TailsmanDesign/PocketMage_PDA/Resources/Assets/Calendar/calendar00.bmp

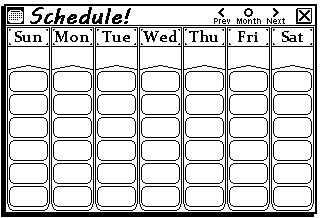
Resources/Assets/Calendar/calendar00.bmp
