TailsmanDesign/PocketMage_PDA/Resources/Assets/Calendar/calendar03.bmp

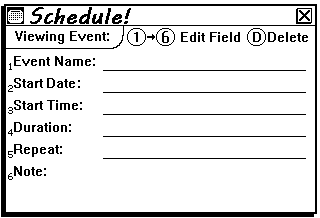
Resources/Assets/Calendar/calendar03.bmp
