TailsmanDesign/PocketMage_PDA/Resources/Assets/Calendar/calendar04.bmp

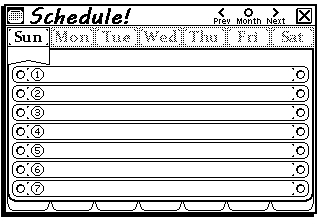
Resources/Assets/Calendar/calendar04.bmp
