TailsmanDesign/PocketMage_PDA/Resources/Assets/File Wizard/fileWiz1.bmp

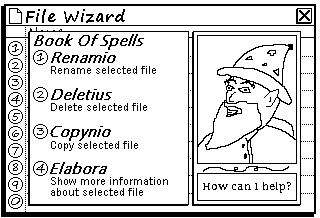
Resources/Assets/File Wizard/fileWiz1.bmp
