TailsmanDesign/PocketMage_PDA/Resources/Assets/File Wizard/fileWiz2.bmp

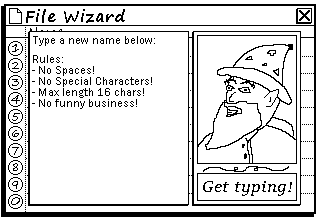
Resources/Assets/File Wizard/fileWiz2.bmp
