TailsmanDesign/PocketMage_PDA/Resources/Assets/File Wizard/fileWizLite0.bmp

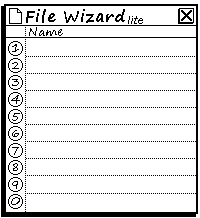
Resources/Assets/File Wizard/fileWizLite0.bmp
