TailsmanDesign/PocketMage_PDA/Resources/Assets/File Wizard/fileWizLite1.bmp

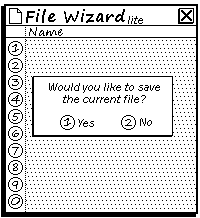
Resources/Assets/File Wizard/fileWizLite1.bmp
