TailsmanDesign/PocketMage_PDA/Resources/Assets/File Wizard/fileWizLite2.bmp

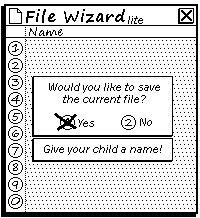
Resources/Assets/File Wizard/fileWizLite2.bmp
