TailsmanDesign/PocketMage_PDA/Resources/Assets/Font Czar/font0.bmp

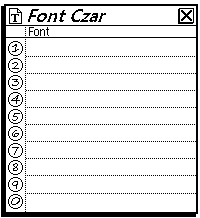
Resources/Assets/Font Czar/font0.bmp
