TailsmanDesign/PocketMage_PDA/Resources/Assets/Onboarding/onboardMage.png

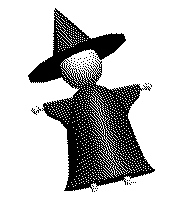
Resources/Assets/Onboarding/onboardMage.png
