TailsmanDesign/PocketMage_PDA/Resources/Assets/ScreenSaver/New folder/appzap_Omiopi.bmp

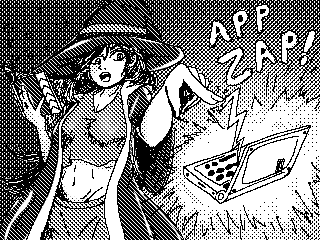
Resources/Assets/ScreenSaver/New folder/appzap_Omiopi.bmp
