TailsmanDesign/PocketMage_PDA/Resources/Assets/ScreenSaver/New folder/betterworld_JosieBB.bmp

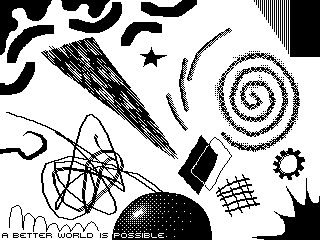
Resources/Assets/ScreenSaver/New folder/betterworld_JosieBB.bmp
