TailsmanDesign/PocketMage_PDA/Resources/Assets/ScreenSaver/New folder/castle_Nora.bmp

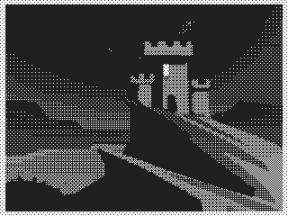
Resources/Assets/ScreenSaver/New folder/castle_Nora.bmp
