TailsmanDesign/PocketMage_PDA/Resources/Assets/ScreenSaver/New folder/chad_rein.bmp

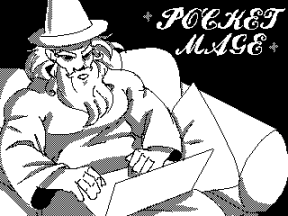
Resources/Assets/ScreenSaver/New folder/chad_rein.bmp
