TailsmanDesign/PocketMage_PDA/Resources/Assets/ScreenSaver/New folder/classic (1).bmp

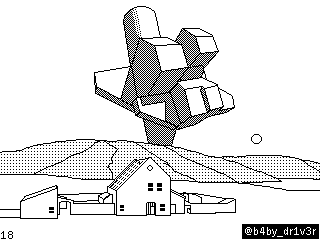
Resources/Assets/ScreenSaver/New folder/classic (1).bmp
