TailsmanDesign/PocketMage_PDA/Resources/Assets/ScreenSaver/New folder/classic (2).bmp

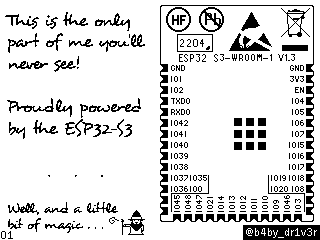
Resources/Assets/ScreenSaver/New folder/classic (2).bmp
