TailsmanDesign/PocketMage_PDA/Resources/Assets/ScreenSaver/New folder/classic (3).bmp

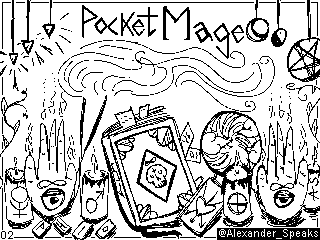
Resources/Assets/ScreenSaver/New folder/classic (3).bmp
