TailsmanDesign/PocketMage_PDA/Resources/Assets/ScreenSaver/New folder/classic (5).bmp

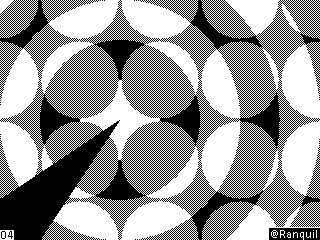
Resources/Assets/ScreenSaver/New folder/classic (5).bmp
