TailsmanDesign/PocketMage_PDA/Resources/Assets/ScreenSaver/New folder/classic (6).bmp

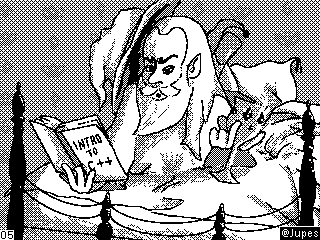
Resources/Assets/ScreenSaver/New folder/classic (6).bmp
