TailsmanDesign/PocketMage_PDA/Resources/Assets/ScreenSaver/New folder/classic (7).bmp

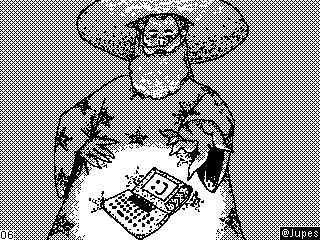
Resources/Assets/ScreenSaver/New folder/classic (7).bmp
