TailsmanDesign/PocketMage_PDA/Resources/Assets/ScreenSaver/New folder/classic (8).bmp

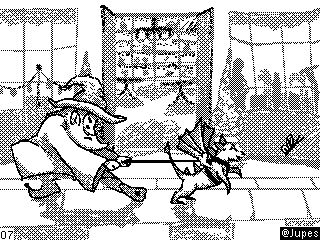
Resources/Assets/ScreenSaver/New folder/classic (8).bmp
