TailsmanDesign/PocketMage_PDA/Resources/Assets/ScreenSaver/New folder/classic (9).bmp

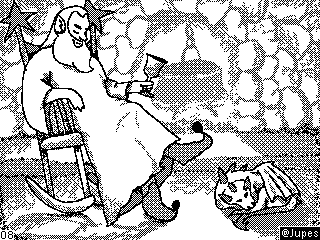
Resources/Assets/ScreenSaver/New folder/classic (9).bmp
