TailsmanDesign/PocketMage_PDA/Resources/Assets/ScreenSaver/New folder/classic (10).bmp

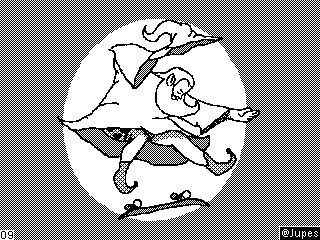
Resources/Assets/ScreenSaver/New folder/classic (10).bmp
