TailsmanDesign/PocketMage_PDA/Resources/Assets/ScreenSaver/New folder/classic (11).bmp

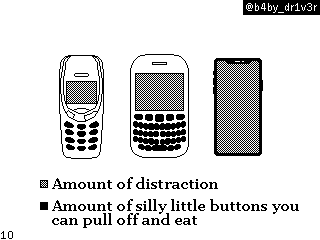
Resources/Assets/ScreenSaver/New folder/classic (11).bmp
