TailsmanDesign/PocketMage_PDA/Resources/Assets/ScreenSaver/New folder/classic (13).bmp

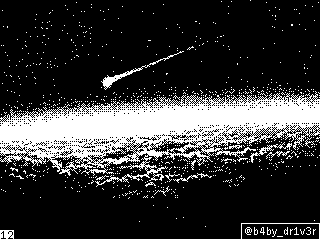
Resources/Assets/ScreenSaver/New folder/classic (13).bmp
