TailsmanDesign/PocketMage_PDA/Resources/Assets/ScreenSaver/New folder/classic (14).bmp

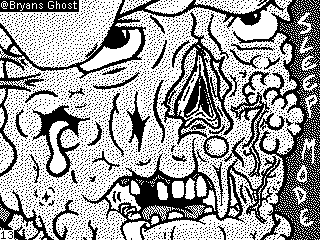
Resources/Assets/ScreenSaver/New folder/classic (14).bmp
