TailsmanDesign/PocketMage_PDA/Resources/Assets/ScreenSaver/New folder/classic (15).bmp

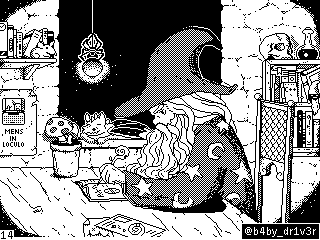
Resources/Assets/ScreenSaver/New folder/classic (15).bmp
