TailsmanDesign/PocketMage_PDA/Resources/Assets/ScreenSaver/New folder/classic (18).bmp

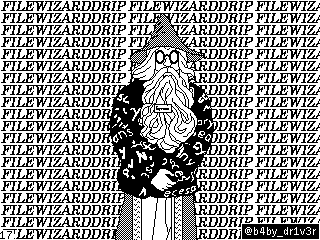
Resources/Assets/ScreenSaver/New folder/classic (18).bmp
