TailsmanDesign/PocketMage_PDA/Resources/Assets/ScreenSaver/New folder/dragon_TheOddFireFox.bmp

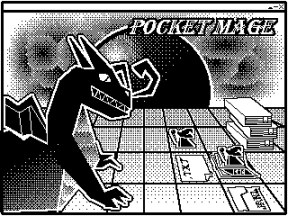
Resources/Assets/ScreenSaver/New folder/dragon_TheOddFireFox.bmp
