TailsmanDesign/PocketMage_PDA/Resources/Assets/ScreenSaver/New folder/mage_GusCosta.bmp

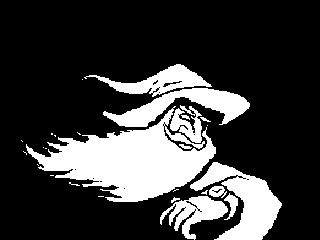
Resources/Assets/ScreenSaver/New folder/mage_GusCosta.bmp
