TailsmanDesign/PocketMage_PDA/Resources/Assets/ScreenSaver/New folder/newtstail_J3.bmp

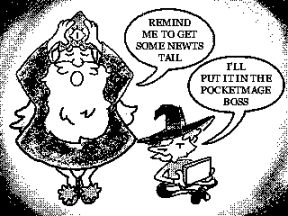
Resources/Assets/ScreenSaver/New folder/newtstail_J3.bmp
