TailsmanDesign/PocketMage_PDA/Resources/Assets/ScreenSaver/New folder/powerbeam_forest927.bmp

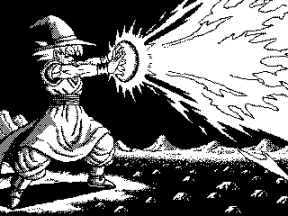
Resources/Assets/ScreenSaver/New folder/powerbeam_forest927.bmp
