TailsmanDesign/PocketMage_PDA/Resources/Assets/ScreenSaver/New folder/powerful_NuclearDuck13.bmp

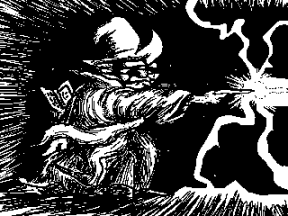
Resources/Assets/ScreenSaver/New folder/powerful_NuclearDuck13.bmp
