TailsmanDesign/PocketMage_PDA/Resources/Assets/ScreenSaver/New folder/scooter_b4by_dr1v3r.bmp

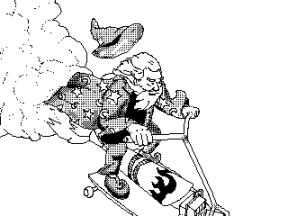
Resources/Assets/ScreenSaver/New folder/scooter_b4by_dr1v3r.bmp
