TailsmanDesign/PocketMage_PDA/Resources/Assets/ScreenSaver/New folder/startrails_Fin.bmp

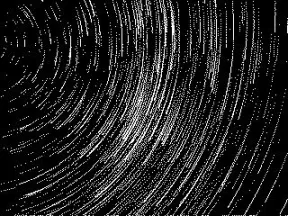
Resources/Assets/ScreenSaver/New folder/startrails_Fin.bmp
