TailsmanDesign/PocketMage_PDA/Resources/Assets/ScreenSaver/New folder/strongwiz_NuclearDuck13.bmp

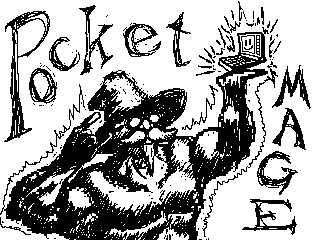
Resources/Assets/ScreenSaver/New folder/strongwiz_NuclearDuck13.bmp
