TailsmanDesign/PocketMage_PDA/Resources/Assets/ScreenSaver/New folder/wizdays_Bryans Ghost.bmp

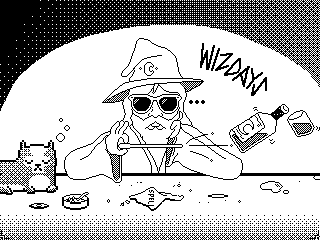
Resources/Assets/ScreenSaver/New folder/wizdays_Bryans Ghost.bmp
