TailsmanDesign/PocketMage_PDA/Resources/Assets/Settings/settings0.bmp

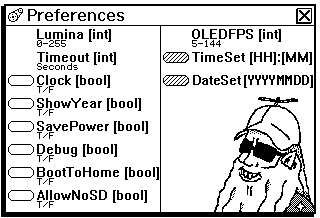
Resources/Assets/Settings/settings0.bmp
