TailsmanDesign/PocketMage_PDA/Resources/Assets/Sleep/sleep0.bmp

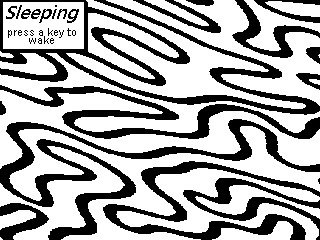
Resources/Assets/Sleep/sleep0.bmp
