TailsmanDesign/PocketMage_PDA/Resources/Assets/Tasks/0.bmp

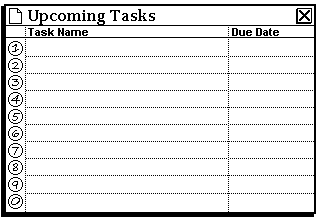
Resources/Assets/Tasks/0.bmp
