TailsmanDesign/PocketMage_PDA/Resources/Assets/Tasks/1.bmp

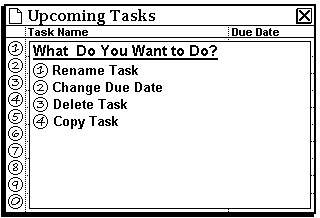
Resources/Assets/Tasks/1.bmp
