TailsmanDesign/PocketMage_PDA/Resources/Assets/Journal/journal0.bmp

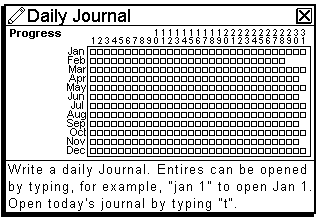
Resources/Assets/Journal/journal0.bmp
